larivera-UVG/Estimulador-Nervio-Vago-2021/Disenos 3D/pin-header-female-double-2-54mm-different-pin-numbers-1.snapshot.2/20-Pin Header - Female - 2.54mm.step

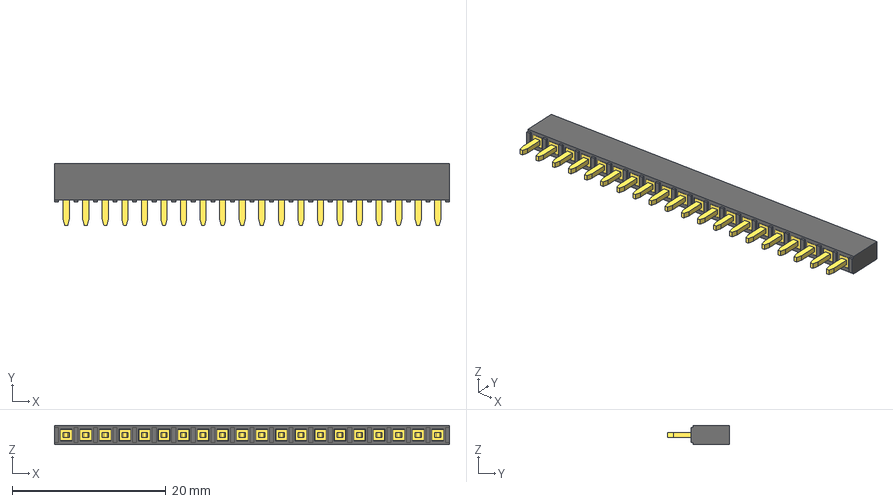
[picture p52: CAD file, 2021-08-09, last stored version]
Disenos 3D/pin-header-female-double-2-54mm-different-pin-numbers-1.snapshot.2/20-Pin Header - Female - 2.54mm.step
51.3 x 8.00 x 2.50 mm
