larivera-UVG/Estimulador-Nervio-Vago-2021/Disenos 3D/pin-header-female-double-2-54mm-different-pin-numbers-1.snapshot.2/12-Pin Header - Female - Double - 2.54mm.step

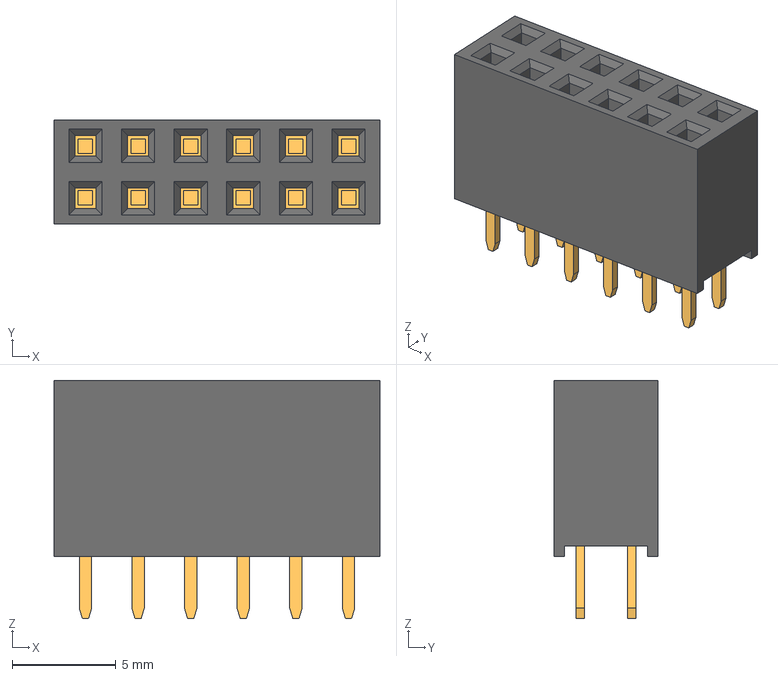
[picture p60: CAD file, 2021-08-09, last stored version]
Disenos 3D/pin-header-female-double-2-54mm-different-pin-numbers-1.snapshot.2/12-Pin Header - Female - Double - 2.54mm.step
15.7 x 5.00 x 11.5 mm
