larivera-UVG/Estimulador-Nervio-Vago-2021/Disenos 3D/pin-header-female-double-2-54mm-different-pin-numbers-1.snapshot.2/22-Pin Header - Female - Double - 2.54mm.step

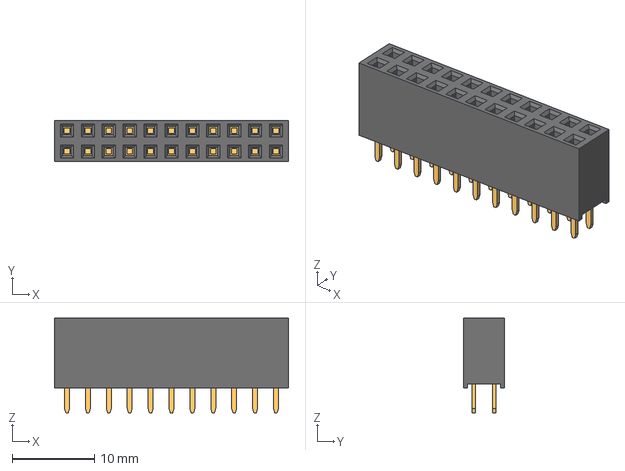
[picture p71: CAD file, 2021-08-09, last stored version]
Disenos 3D/pin-header-female-double-2-54mm-different-pin-numbers-1.snapshot.2/22-Pin Header - Female - Double - 2.54mm.step
28.4 x 5.00 x 11.5 mm
