larivera-UVG/Estimulador-Nervio-Vago-2021/Modulo Estimulador/Pruebas de Neuroestimulacion/Simulacion Nervio Vago.asc

C1: cap; 10µ
C2: cap; 10µ
C3: cap; 10µ
C4: cap; 10µ
C5: cap; 10µ
C6: cap; 10µ
C7: cap; 10µ
Estimulador_5: current; PULSE(0 1.25m 0 0 0 .75m 1.5m)
Estimulador_S: current; PULSE(0 .25mA 0 0 0 .13m .26m)
R1: res; 33k
R2: res; 33k
R3: res; 33k
R4: res; 33k
R5: res; 33k
R6: res; 33k
R7: res; 10k
R8: res; 10k
R9: res; 10k
R10: res; 10k
R11: res; 10k
R12: res; 10K
R13: res; 33k
R14: res; 10k
Named nets: 0, Entrada, 1cm, 2cm, 3cm, 4cm, 5cm
.tran 2040u
