larivera-UVG/Estimulador-Nervio-Vago-2021/Modulo Estimulador/Codigos para pruebas de comunicacion/Prubas basicas de diagnostico/Esp_transmitter/Esp_transmitter.ino

#include <SPI.h>
#include <nRF24L01.h>
#include <RF24.h>
RF24 radio(2, 0); // CE, CSN         
const byte address[6] = "00001";     //Byte of array representing the address. This is the address where we will send the data. This should be same on the receiving side.
int button_pin = 3;
boolean button_state = 0;
void setup() {
pinMode(button_pin, INPUT);
radio.begin();                  //Starting the Wireless communication
radio.openWritingPipe(address); //Setting the address where we will send the data
radio.setPALevel(RF24_PA_MIN);  //You can set it as minimum or maximum depending on the distance between the transmitter and receiver.
radio.stopListening();          //This sets the module as transmitter
}
void loop()
{
button_state = digitalRead(button_pin);
if(button_state == HIGH)
{
const char text[] = "Your Button State is HIGH";
radio.write(&text, sizeof(text));                  //Sending the message to receiver
}
else
{
const char text[] = "Your Button State is LOW";
radio.write(&text, sizeof(text));                  //Sending the message to receiver dad
}
radio.write(&button_state, sizeof(button_state));  //Sending the message to receiver 
delay(1000);
}
